TomNisbet/TommyPROM/docs/_docs/images/SST39SF-boards.jpg

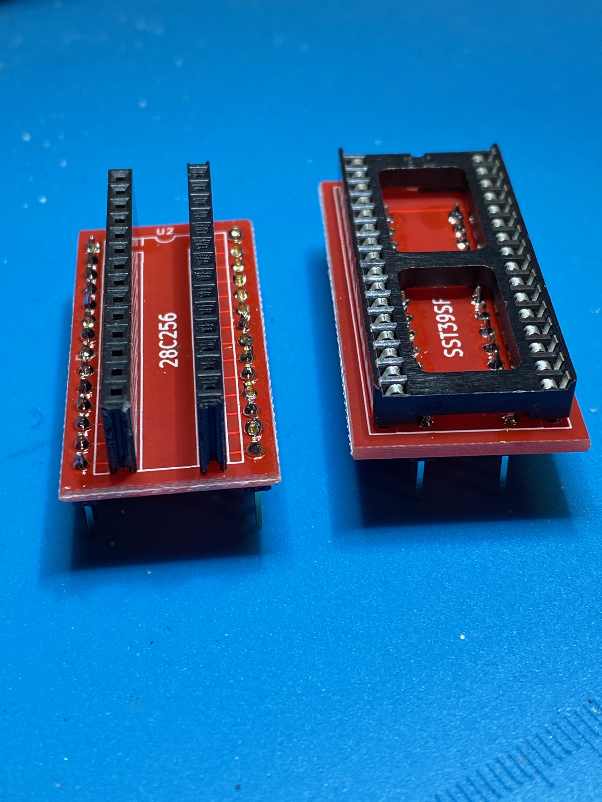
docs/_docs/images/SST39SF-boards.jpg
