TomNisbet/TommyPROM/docs/_docs/images/SST39SF-stacked.jpg

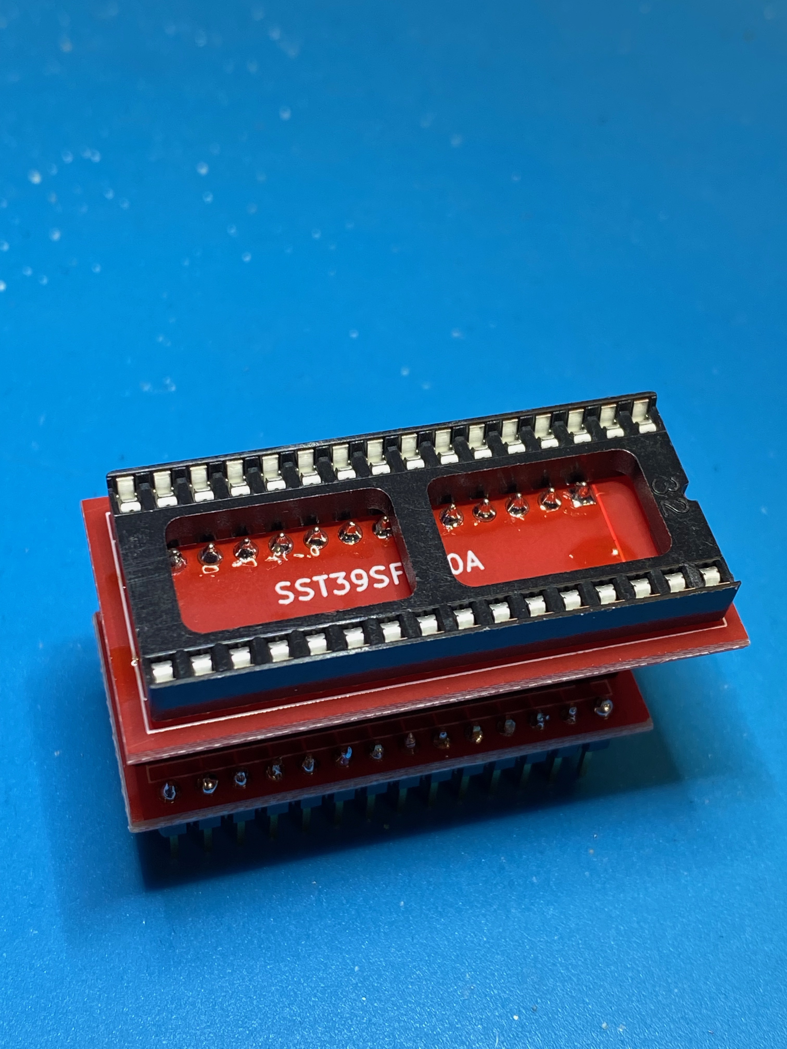
docs/_docs/images/SST39SF-stacked.jpg
