TomNisbet/TommyPROM/docs/_docs/images/TommyPROM32-28C256.jpg

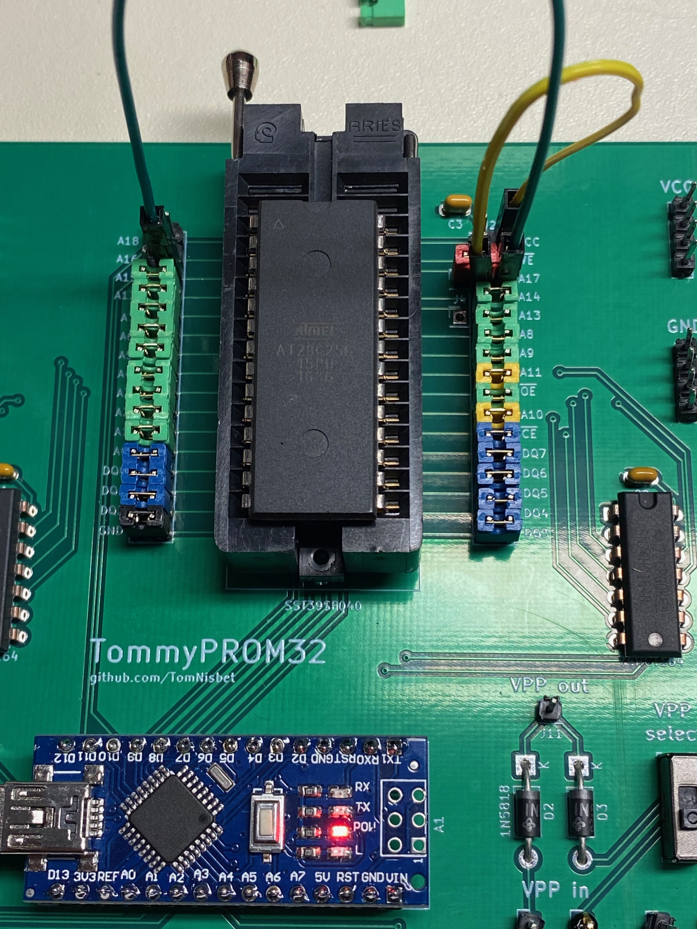
docs/_docs/images/TommyPROM32-28C256.jpg
