TomNisbet/TommyPROM/docs/_docs/images/TommyPROM-595.jpg

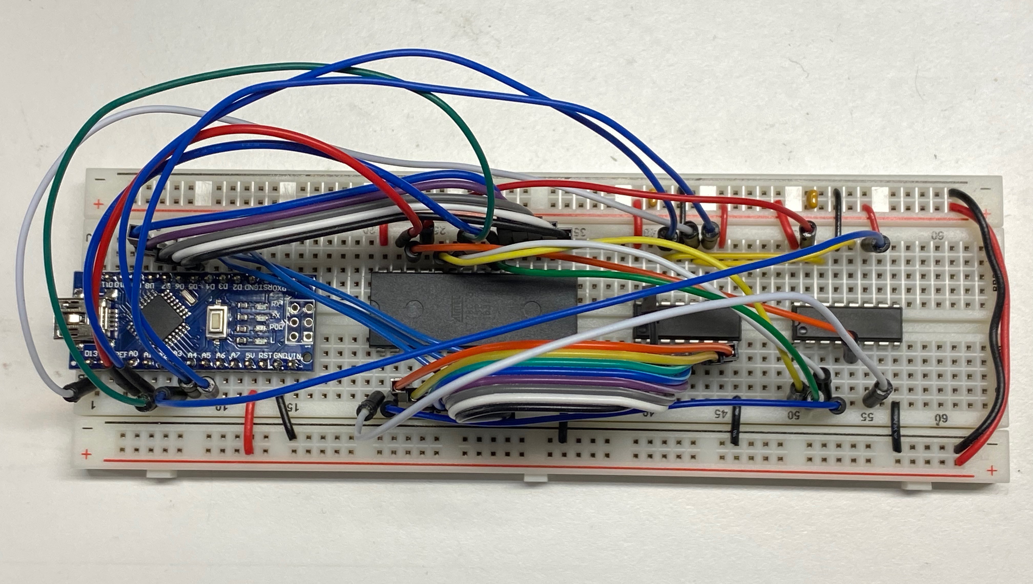
docs/_docs/images/TommyPROM-595.jpg
