TomNisbet/TommyPROM/hardware/TommyPROM-nano.sch

## EAGLE design hardware/TommyPROM-nano.sch (2017-02-28)

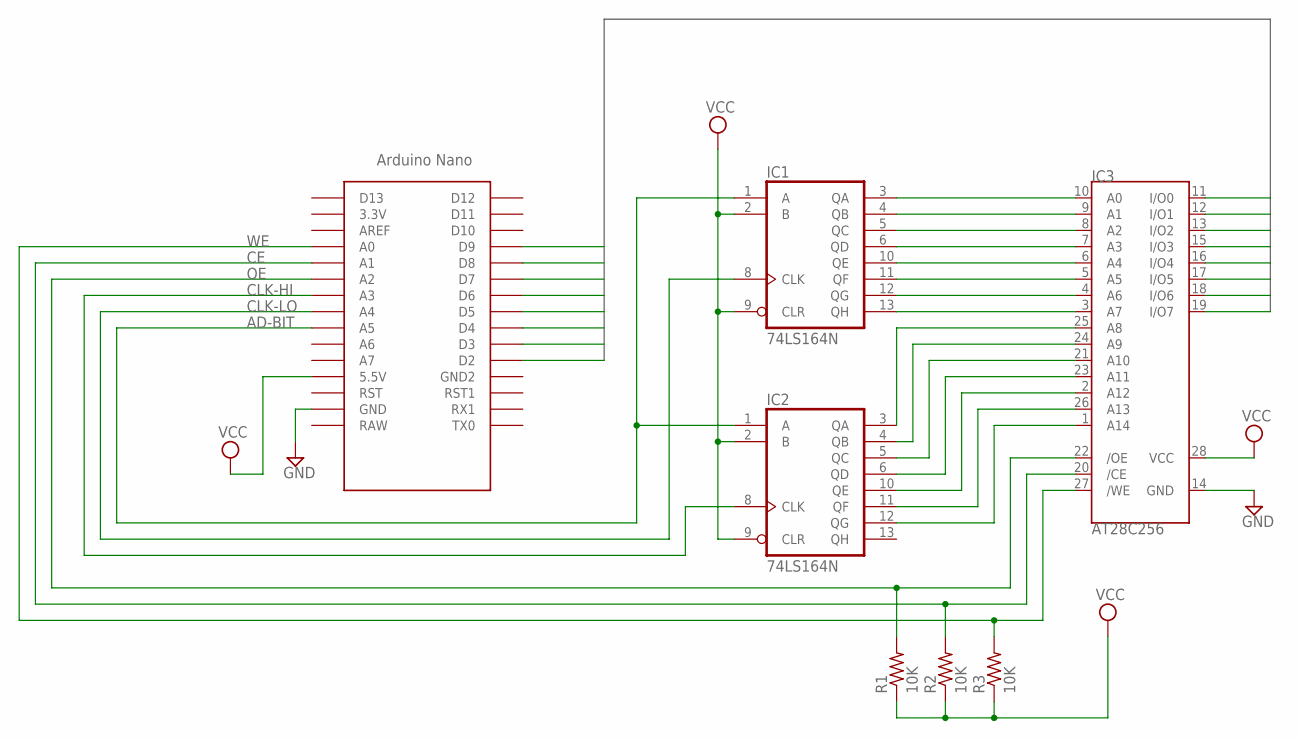
[picture p47: schematic TommyPROM-nano.sch]

Parts:
IC1, IC2: 74LS164N; DIL14
IC3: AT28C256; DIL28-6
R1, R2, R3: 10K; 0204/5
U$2: NANO

Connections:
AD-BIT: IC1.1 (A), IC2.1 (A)
CE: IC3.20 (/CE), R2.2
CLK-HI: IC2.8 (CLK)
CLK-LO: IC1.8 (CLK)
D0: IC3.11 (I/O0)
D1: IC3.12 (I/O1)
D2: IC3.13 (I/O2)
D3: IC3.15 (I/O3)
D4: IC3.16 (I/O4)
D5: IC3.17 (I/O5)
D6: IC3.18 (I/O6)
D7: IC3.19 (I/O7)
GND: IC3.14 (GND)
unnamed: IC2.12 (QG), IC3.1 (A14)
unnamed: IC2.11 (QF), IC3.26 (A13)
unnamed: IC2.10 (QE), IC3.2 (A12)
unnamed: IC2.6 (QD), IC3.23 (A11)
unnamed: IC2.5 (QC), IC3.21 (A10)
unnamed: IC2.4 (QB), IC3.24 (A9)
unnamed: IC2.3 (QA), IC3.25 (A8)
unnamed: IC1.13 (QH), IC3.3 (A7)
unnamed: IC1.12 (QG), IC3.4 (A6)
unnamed: IC1.11 (QF), IC3.5 (A5)
unnamed: IC1.10 (QE), IC3.6 (A4)
unnamed: IC1.6 (QD), IC3.7 (A3)
unnamed: IC1.5 (QC), IC3.8 (A2)
unnamed: IC1.4 (QB), IC3.9 (A1)
unnamed: IC1.3 (QA), IC3.10 (A0)
OE: IC3.22 (/OE), R1.2
VCC: IC1.2 (B), IC1.9 (CLR), IC2.2 (B), IC2.9 (CLR), IC3.28 (VCC), R1.1, R2.1, R3.1
WE: IC3.27 (/WE), R3.2
